Plzsay23/ze-ri/config/vla/references/pick_mask/final_ep_0000.png

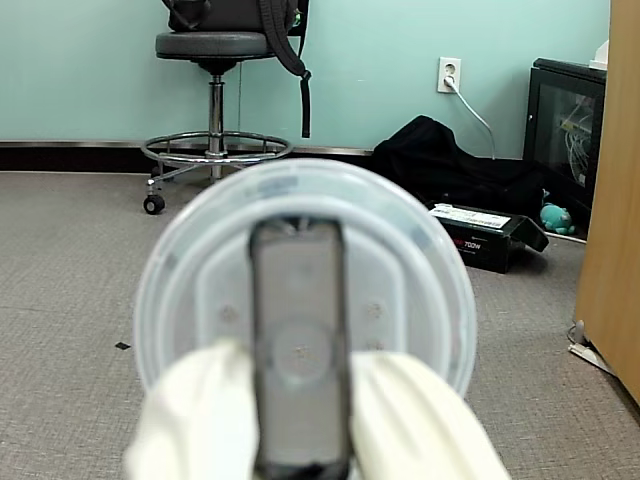
config/vla/references/pick_mask/final_ep_0000.png
