Plzsay23/ze-ri/config/vla/references/pick_mask/final_ep_0022.png

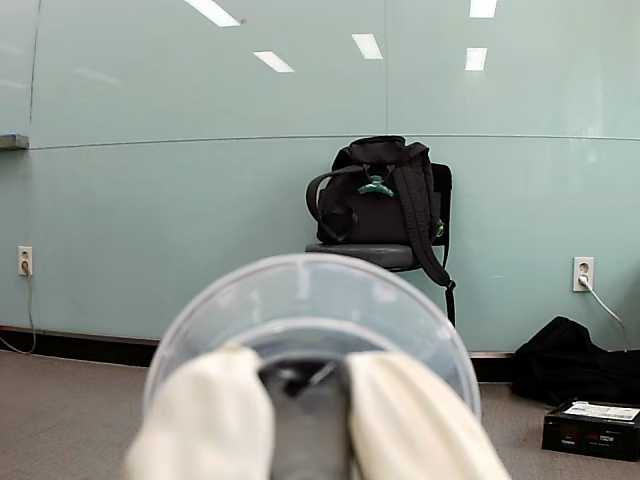
config/vla/references/pick_mask/final_ep_0022.png
