Plzsay23/ze-ri/config/vla/references/pick_wt/final_ep_0002.png

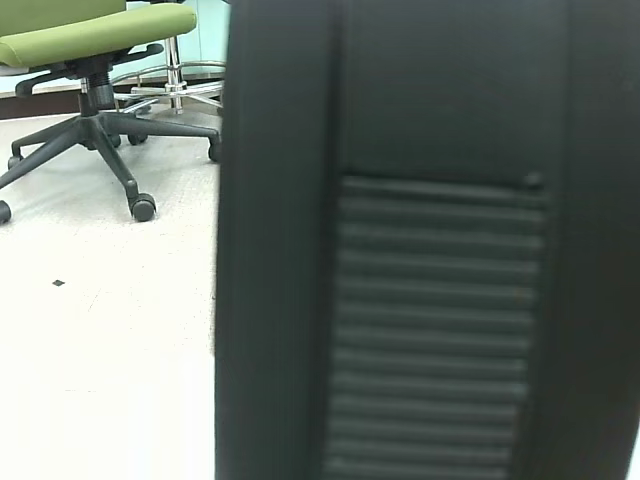
config/vla/references/pick_wt/final_ep_0002.png
