Plzsay23/ze-ri/config/vla/references/pick_wt/final_ep_0006.png

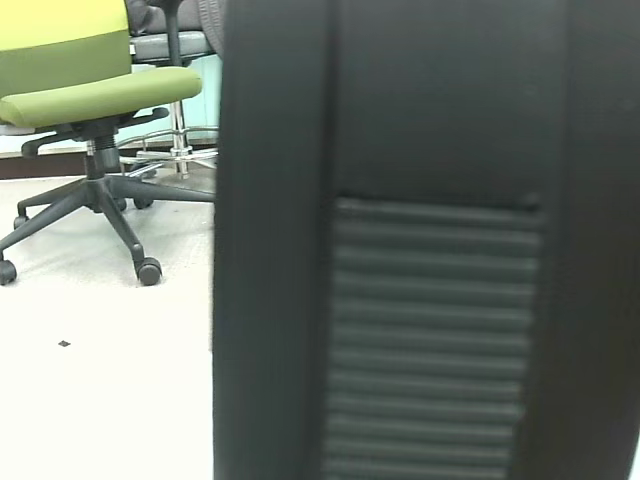
config/vla/references/pick_wt/final_ep_0006.png
