Plzsay23/ze-ri/config/vla/references/pick_wt/final_ep_0013.png

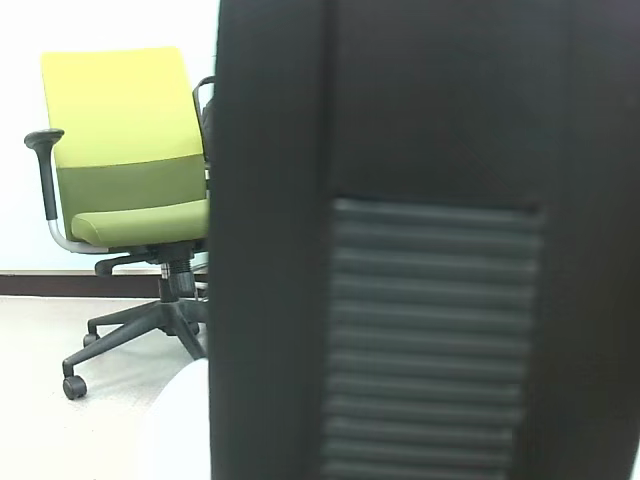
config/vla/references/pick_wt/final_ep_0013.png
