Plzsay23/ze-ri/config/vla/references/pick_wt/final_ep_0017.png

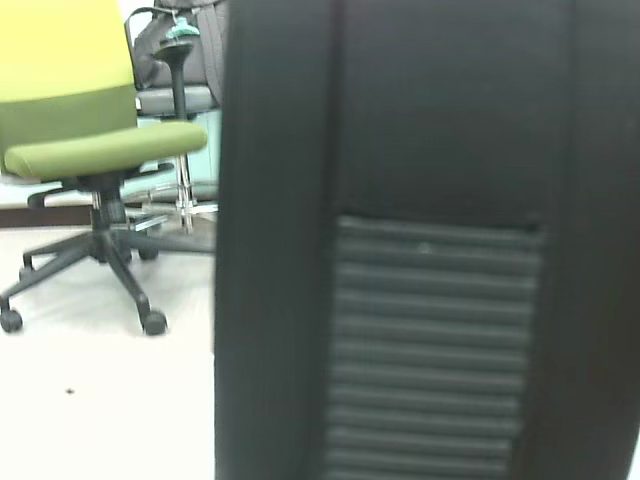
config/vla/references/pick_wt/final_ep_0017.png
