Plzsay23/ze-ri/stl/mount/Mount_battery_12v.stl

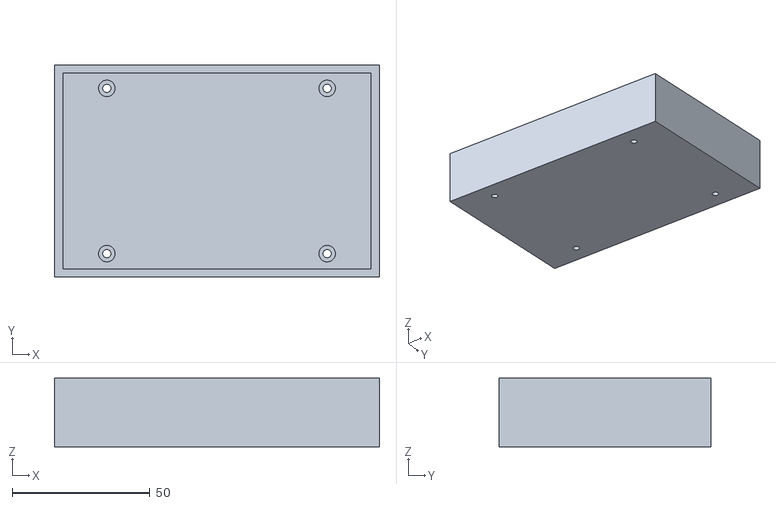
[picture p74: CAD file, 2026-05-06]
stl/mount/Mount_battery_12v.stl
118.0 x 77.0 x 25.0
