Plzsay23/ze-ri/stl/mount/Mount_microphone.stl

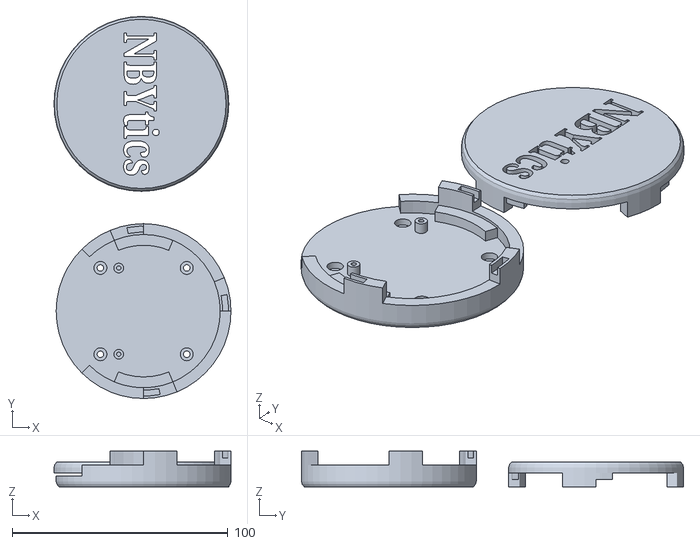
[picture p75: CAD file, 2026-05-06]
stl/mount/Mount_microphone.stl
82.0 x 177.0 x 16.5
