Plzsay23/ze-ri/debug/yolo_handoff/20260604_193615_raw.jpg

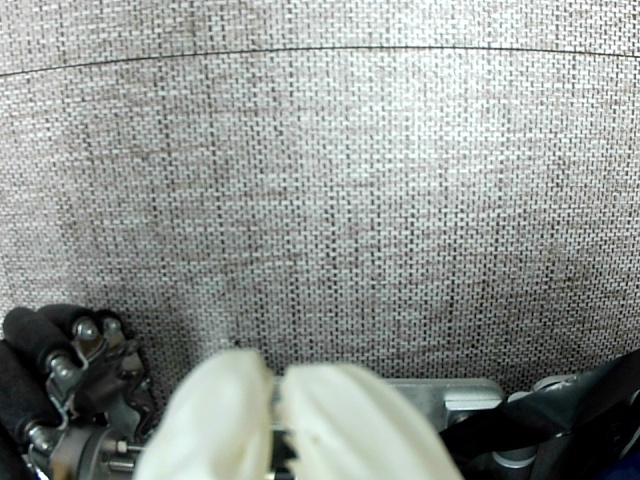
debug/yolo_handoff/20260604_193615_raw.jpg
