Plzsay23/ze-ri/debug/yolo_handoff/20260604_195928_yolo.jpg

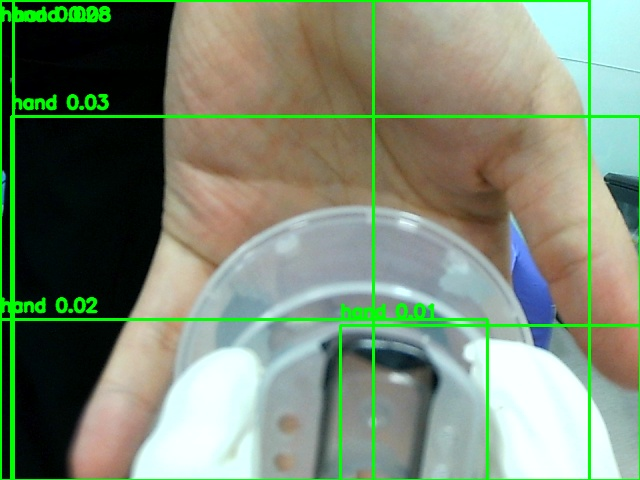
debug/yolo_handoff/20260604_195928_yolo.jpg
